Sector67/nsa-away-hardware/firmware/Random_Test/Random_Test.ino

/*
 * SN74HC165N_shift_reg
 * http://playground.arduino.cc/Code/ShiftRegSN74HC165N
*/

/* How many shift register chips are daisy-chained.
*/
#define NUMBER_OF_SHIFT_CHIPS   1

/* Width of data (how many ext lines).
*/
#define DATA_WIDTH   NUMBER_OF_SHIFT_CHIPS * 8

/* Width of pulse to trigger the shift register to read and latch.
*/
#define PULSE_WIDTH_USEC   5

/* Optional delay between shift register reads.
*/
#define POLL_DELAY_MSEC   1

/* You will need to change the "int" to "long" If the
 * NUMBER_OF_SHIFT_CHIPS is higher than 2.
*/
#define BYTES_VAL_T unsigned int

int ploadPin        = 2;  // Connects to Parallel load pin the 165
int dataPin         = 1; // Connects to the Q7 pin the 165
int clockPin        = 0; // Connects to the Clock pin the 165

BYTES_VAL_T pinValues;
BYTES_VAL_T oldPinValues;

/* This function is essentially a "shift-in" routine reading the
 * serial Data from the shift register chips and representing
 * the state of those pins in an unsigned integer (or long).
*/
BYTES_VAL_T read_shift_regs()
{
    long bitVal;
    BYTES_VAL_T bytesVal = 0;

    /* Trigger a parallel Load to latch the state of the data lines,
    */
    digitalWrite(ploadPin, LOW);
    delayMicroseconds(PULSE_WIDTH_USEC);
    digitalWrite(ploadPin, HIGH);

    /* Loop to read each bit value from the serial out line
     * of the SN74HC165N.
    */
    for(int i = 0; i < DATA_WIDTH; i++)
    {
        bitVal = digitalRead(dataPin);

        /* Set the corresponding bit in bytesVal.
        */
        bytesVal |= (bitVal << ((DATA_WIDTH-1) - i));

        /* Pulse the Clock (rising edge shifts the next bit).
        */
        digitalWrite(clockPin, HIGH);
        delayMicroseconds(PULSE_WIDTH_USEC);
        digitalWrite(clockPin, LOW);
    }

    return(bytesVal);
}

/* Dump the list of zones along with their current status.
*/
void display_pin_values_hex()
{
    Keyboard.println(pinValues, HEX);
}

void setup()
{
    Keyboard.begin();

    /* Initialize our digital pins...
    */
    pinMode(ploadPin, OUTPUT);
    pinMode(clockPin, OUTPUT);
    pinMode(dataPin, INPUT);

    digitalWrite(clockPin, LOW);
    digitalWrite(ploadPin, HIGH);
}

void loop()
{
    /* Read the state of all zones.
    */
    pinValues = read_shift_regs();
    display_pin_values_hex();
    delay(POLL_DELAY_MSEC);
}
